2tn/Meister_2016/基板/elecrow/all.brd

## EAGLE design 基板/elecrow/all.brd (2018-05-12)

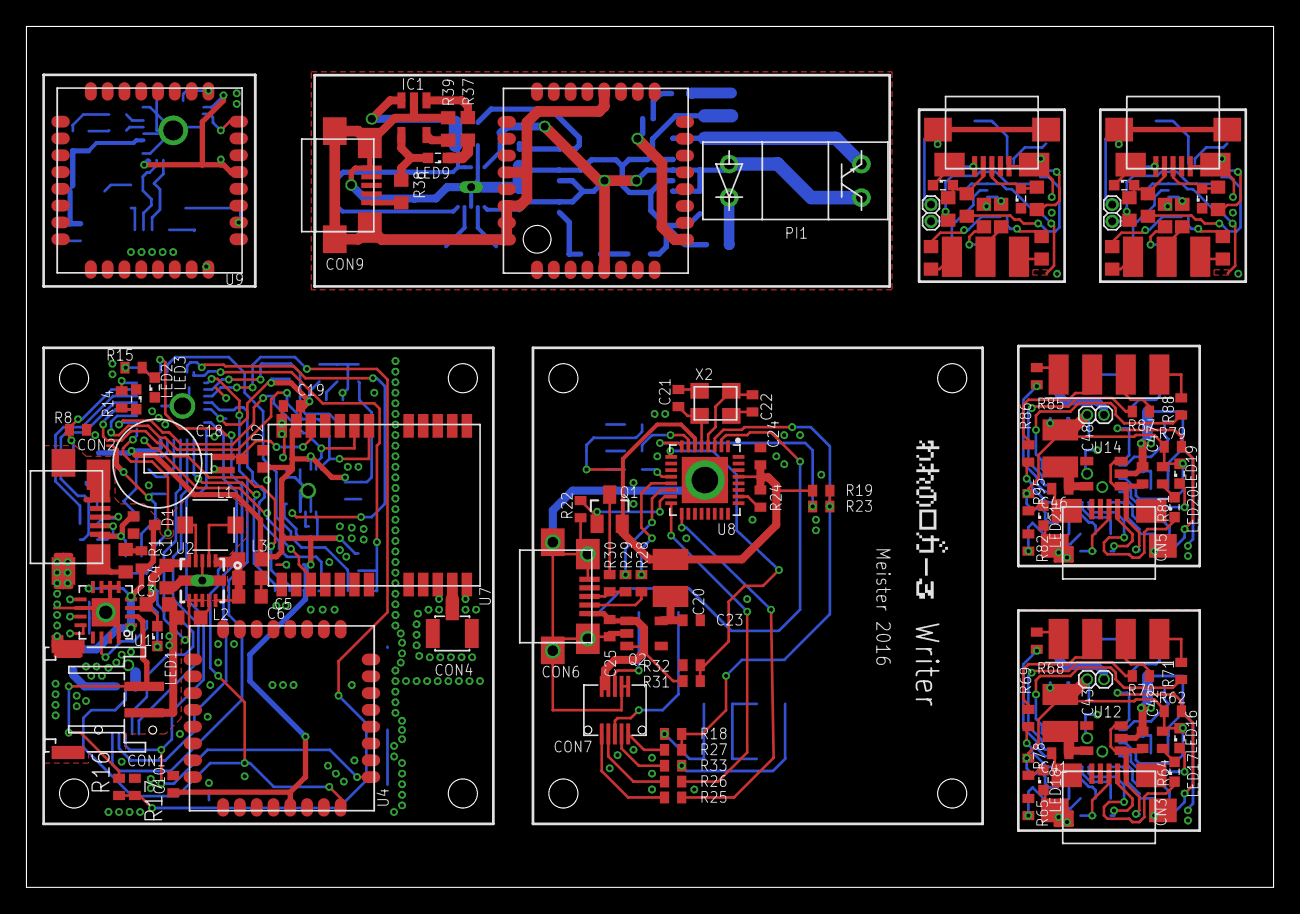
[picture p30: board all.brd from above]

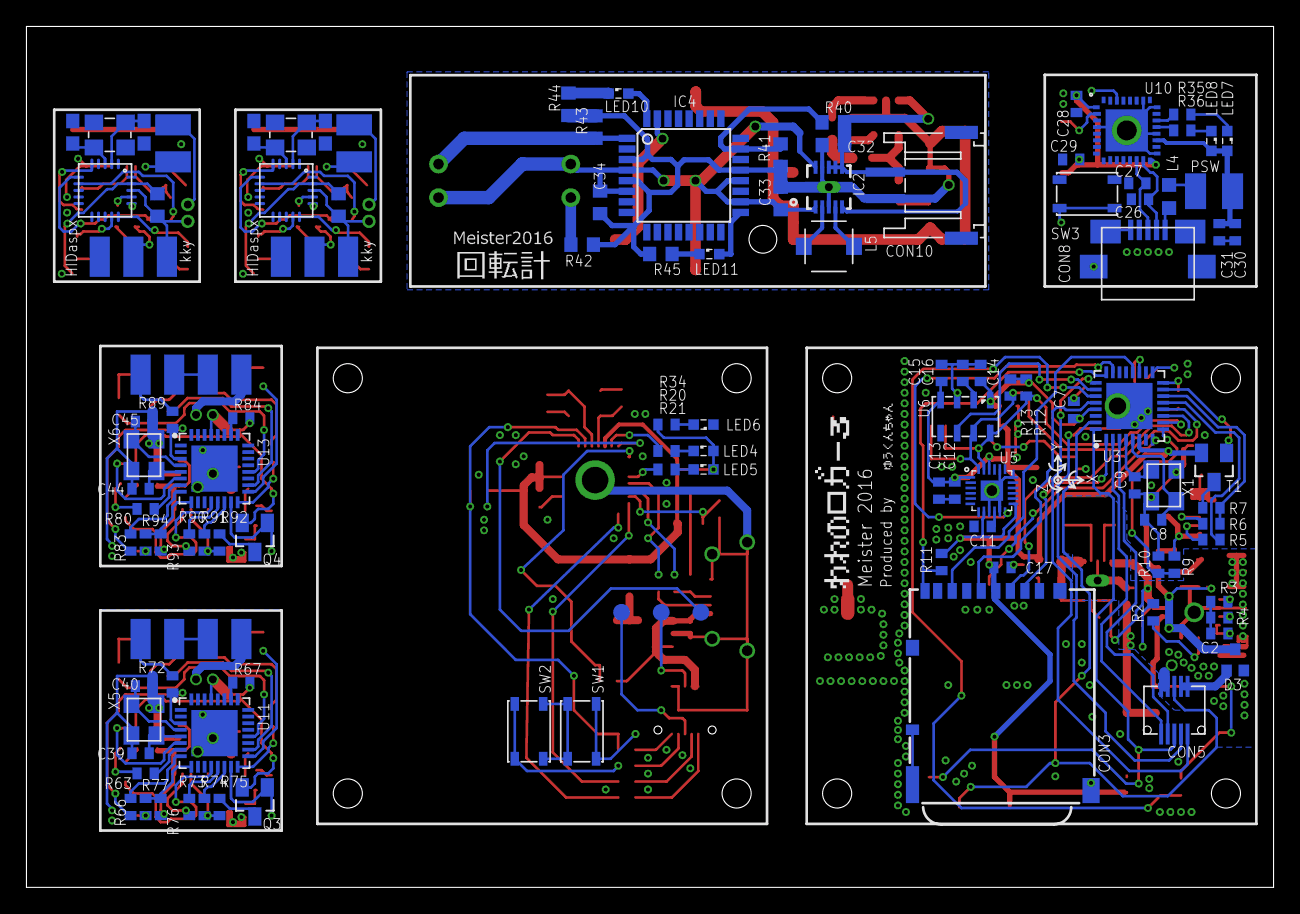
[picture p31: board all.brd from below]

Board: 2 copper layers, 94.3 x 65.1 mm, 236 parts (113 on the bottom side), 217 nets.

Parts:
C1, C3, C4, C5, C6, C32, C33: 10u; 0603
C2: 0.2u; 0402
C7, C10, C11, C12, C14, C16, C17, C19: 0.1u; 0402
C8, C9, C26, C27, C28, C29, C30, C31: 0402
C13: 10n; 0402
C15: 10u; 0402
C18: DCK-3R3E224-E
C20, C43, C48: PSW; C3225
C21, C22, C39, C40, C44, C45: 8P; C0402
C23, C25, C41, C42, C46, C47: 1u; C0402
C24: 0.1u; C0402
C34: 0.1u; 0603
C35, C36, C37, C38: 22p; C0603
CN1, CN2, CN3, CN5: ZX62R-B-5P; MICRO-B
CN4, CN6: 2X4SMD
CON1, CON10: JST-PH2
CON2, CON6, CON8, CON9: ZX62R-B-5P; MICRO-B
CON3: DM3AT-SF-PEJM5SMD; DM3AT-SF-PEJM5
CON4: U.FL; U.FL-R-SMT-1
CON5: DF12#-10DS; DF12A-10DS
CON7: DF12#-10DP; DF12D-10DP
D1, D2, D3: RB461F; UMD3
IC1: TSOT23-5
IC2: S-PVSON-N10
IC3: LITESMD; LITE
IC4: ATMEGA48/88/168-AU; TQFP32-08
JP1, JP2: 1X02/HALF
JP3, JP4: 1X02/HARF
L1, L5: 2.2u; VLF4012ST
L2, L3: BLM; C0603K
L4: C0603K
LED1, LED2, LED3, LED4, LED5, LED6, LED7, LED8, LED9, LED10, LED11, LED16, LED17, LED18, LED19, LED20, LED21: SML0603
LED12, LED13, LED14, LED15: BLUE; SML0603
PI1: RPI-574
PSW, PSW1, PSW2: 100m; C3225
Q1, Q3, Q4: PDTA114ET; SOT23
Q2: MIC550X; SOT23_5PIN
R1: 1; 0402
R2, R14, R15: 100; 0402
R3: 105k; 0402
R4: 124k; 0402
R5, R6: 33; 0402
R7: 1.5k; 0402
R8, R10: 10k; 0402
R9: 5.6k; 0402
R11, R12, R13: 4.7k; 0402
R16: 3.3k; 0402
R17: 2.2k; 0402
R18, R23, R25, R26, R27, R33, R66, R68, R69, R70, R71, R72, R83, R85, R86, R87, R88, R89: 270; R0402
R19, R22, R24, R32, R62, R65, R67, R77, R79, R82, R84, R94: 10k; R0402
R20, R21, R30, R63, R64, R75, R80, R81, R92: 1.5k; R0402
R28, R29, R73, R74, R90, R91: 33; R0402
R31, R76, R93: 5.6k; R0402
R34, R78, R95: 750; R0402
R35, R36: R0402
R37: 100; 0603
R38: 0.25; 0603
R39: 3.2k; 0603
R40: 3.3k; 0603
R41: 2.2k; 0603
R42, R44, R45: 200; 0603
R43: 1.0M; 0603
R46, R54: 2.2k; R0603
R47, R48, R55, R56: 75; R0603
R49, R57: 10k; R0603
R50, R51, R52, R53, R58, R59, R60, R61: 100; R0603
SW1, SW2, SW3: SKRPACE010
T1: PDTA114ET; SOT23
U1: LTC4055; QFN16
U2: TPS6300XDRCT; S-PVSON-N10
U3, U8, U11, U13: LPC11U35FHI33/501; SOT617-3
U4, U9: TWE-LITE_SMD; LITE
U5: MPU-9250
U6: MPL3115A2
U7: NEO-7M
U10: FT232RQ; QFN32
U12, U14: MIC550X; SOT23_5PIN
U$1: DIRECTION
U$2, U$3, U$4: TESTPAD
U$5, U$7: TINY2313-*M*; MLF20
U$6, U$8: AVR-ISP-6-EDGE; 6PAD_ISP
X1, X2, X3, X4, X5, X6: FA238V; V66RA

Connections:
!RESET!: CON5.10, U3.2
!USB_CONNECT!: R8.2, T1.1, U3.15
!USB_CONNECT!1: Q1.1, R22.2, U8.15
!USB_CONNECT!2: Q3.1, R65.2, U11.15
!USB_CONNECT!3: Q4.1, R82.2, U13.15
+3V1: C28.1, C29.1, U9.5, U10.1, U10.16
+3V2: C33.1, C34.1, IC2.1, IC2.10, IC3.5, IC4.4, IC4.6, IC4.18, IC4.20, PI1.DA, PI1.TC
+3V3: C7.1, C10.1, C12.1, C13.1, C14.1, C15.1, C17.1, C19.1, CON3.4, D2.2, L3.1, R11.2, R12.2, R13.2, T1.2, U3.6, U3.29, U4.5, U5.1, U5.8, U5.13, U5.22, U6.1, U6.4, U7.23
+5V: D1.3, D3.3, R1.2, U1.1, U1.4, U1.8
+5V1: C30.1, C31.1, LED7.A, LED8.A, PSW.1, U10.19
AD7: R16.1, R17.2, U3.27
BOOT: CON7.8, R33.2
D+USB: CON6.3, R29.2, R30.1
D+USB1: CN3.3, R74.2, R75.1
D+USB2: CN5.3, R91.2, R92.1
D-USB: CON6.2, R28.2
D-USB1: CN3.2, R73.2
D-USB2: CN5.2, R90.2
GND: C5.2, C6.2, C7.2, C8.2, C9.2, C10.2, C11.2, C12.2, C13.2, C14.2, C15.2, C16.2, C17.2, C18.1, C19.2, CON3.6, CON3.10, CON3.P$10, CON3.P$11, CON3.P$12, CON3.P$14, CON4.1, CON4.2, L2.2, LED2.C, LED3.C, R8.1, R10.1, R17.1, U2.9, U3.33, U4.20, U4.28, U4.30, U4.31, U4.32, U5.9, U5.11, U5.18, U5.20, U5.PAD, U6.3, U7.10, U7.12, U7.13, U7.24, X1.P2GND, X1.P4GND
GND1: C21.2, C22.2, C23.2, C24.2, C25.2, CON6.5, CON6.CASE@1, CON6.CASE@2, CON6.CASE@3, CON6.CASE@4, CON7.7, CON7.9, LED6.C, Q2.2, R22.1, R32.1, SW1.1, SW1.2, SW2.1, SW2.2, U8.33, X2.P2GND, X2.P4GND
GND2: C26.2, C27.2, C28.2, C29.2, C30.2, C31.2, CON8.5, CON8.CASE@1, CON8.CASE@2, CON8.CASE@3, CON8.CASE@4, SW3.1, SW3.2, U9.20, U9.28, U9.30, U9.31, U9.32, U10.4, U10.17, U10.20, U10.24, U10.26, U10.PAD
GND3: C32.2, C33.2, C34.2, CON9.5, CON9.CASE@1, CON9.CASE@2, CON9.CASE@3, CON9.CASE@4, CON10.1, IC1.2, IC2.3, IC2.9, IC2.PAD, IC2.PAD@1, IC3.20, IC3.28, IC3.30, IC3.31, IC3.32, IC4.3, IC4.5, IC4.21, R39.1, R41.1, R42.1, R43.2, R44.1, R45.1
GND4: C35.2, C36.2, CN1.5, CN1.CASE@1, CN1.CASE@2, CN1.CASE@3, CN1.CASE@4, LED12.C, LED13.C, U$5.P$8, U$6.GND, X3.P2GND, X3.P4GND
GND5: C37.2, C38.2, CN2.5, CN2.CASE@1, CN2.CASE@2, CN2.CASE@3, CN2.CASE@4, LED14.C, LED15.C, U$7.P$8, U$8.GND, X4.P2GND, X4.P4GND
GND6: C39.2, C40.2, C41.2, C42.2, CN3.5, CN3.CASE@1, CN3.CASE@2, CN3.CASE@3, CN3.CASE@4, CN4.3, CN4.5, LED18.C, R65.1, R77.1, U11.33, U12.2, X5.P2GND, X5.P4GND
GND7: C44.2, C45.2, C46.2, C47.2, CN5.5, CN5.CASE@1, CN5.CASE@2, CN5.CASE@3, CN5.CASE@4, CN6.3, CN6.5, LED21.C, R82.1, R94.1, U13.33, U14.2, X6.P2GND, X6.P4GND
MISO1: CON3.7, U3.20
MISO2: R59.1, U$7.P$15
MISO3: R51.1, U$5.P$15
MOSI1: CON3.3, U3.12
MOSI2: R58.2, U$7.P$16
MOSI3: R50.2, U$5.P$16
unnamed: C8.1, U3.5, X1.P1X1
unnamed: CON2.2, R5.1
unnamed: C9.1, U3.4, X1.P3X2
unnamed: CON2.3, R6.1
unnamed: R7.2, T1.3
unnamed: LED3.A, R15.1
unnamed: CON4.3, U7.11
unnamed: C16.1, U6.2
unnamed: L1.2, U2.2
unnamed: C11.1, U5.10
unnamed: L1.1, U2.4
unnamed: LED2.A, R14.1
unnamed: C21.1, U8.5, X2.P1X1
unnamed: C22.1, U8.4, X2.P3X2
unnamed: R29.1, U8.14
unnamed: C1.1, R1.1
unnamed: C5.1, C6.1, L3.2, U2.1, U2.10
unnamed: CON5.1, CON5.3, D3.2
unnamed: R3.2, U1.9
unnamed: R4.2, U1.11
unnamed: C2.1, U1.12
unnamed: R2.1, U1.14
unnamed: LED1.C, R2.2
unnamed: C3.1, C4.1, LED1.A, U1.3, U2.5, U2.6, U2.7, U2.8
unnamed: CON1.1, R16.2, U1.2
unnamed: C18.2, D2.3, U7.22
unnamed: R28.1, U8.13
unnamed: Q1.3, R30.2
unnamed: CON7.2, R25.1
unnamed: CON7.4, R26.1
unnamed: LED6.A, R34.2
unnamed: LED4.C, R20.1
unnamed: C20.2, C23.1, Q2.5
unnamed: CON7.10, R27.1
unnamed: R18.1, SW1.3, SW1.4
unnamed: R33.1, SW2.3, SW2.4
unnamed: U8.2, U$4.P$1
unnamed: LED5.C, R21.1
unnamed: C26.1, CON8.2, U10.15
unnamed: C27.1, CON8.3, U10.14
unnamed: CON8.1, L4.2
unnamed: U9.9, U10.30
unnamed: U9.8, U10.2
unnamed: L4.1, PSW.2
unnamed: LED7.C, R35.2
unnamed: LED8.C, R36.2
unnamed: R35.1, U10.22
unnamed: R36.1, U10.21
unnamed: SW3.3, SW3.4, U9.2
unnamed: IC1.4, LED9.A, R38.2
unnamed: IC1.1, R37.2
unnamed: LED9.C, R37.1
unnamed: IC2.4, L5.1
unnamed: IC2.2, L5.2
unnamed: CON9.1, R38.1
unnamed: IC1.5, R39.2
unnamed: IC4.23, R40.1, R41.2
unnamed: IC4.1, PI1.TE, R43.1
unnamed: PI1.DC, R42.2
unnamed: IC4.17, LED11.A
unnamed: LED11.C, R45.2
unnamed: IC4.32, LED10.A
unnamed: LED10.C, R44.2
unnamed: C36.1, U$5.P$2, X3.P1X1
unnamed: C35.1, U$5.P$3, X3.P3X2
unnamed: CN1.1, PSW1.2
unnamed: CN1.2, LED13.A, R46.2, R47.2
unnamed: CN1.3, LED12.A, R48.2
unnamed: R46.1, U$5.P$7
unnamed: R47.1, U$5.P$6
unnamed: R48.1, U$5.P$5
unnamed: R49.2, U$5.P$19
unnamed: R52.2, U$6.SCK
unnamed: R51.2, U$6.MISO
unnamed: R53.2, U$6.RST
unnamed: R50.1, U$6.MOSI
unnamed: JP1.2, PSW1.1
unnamed: C38.1, U$7.P$2, X4.P1X1
unnamed: C37.1, U$7.P$3, X4.P3X2
unnamed: CN2.1, PSW2.2
unnamed: CN2.2, LED15.A, R54.2, R55.2
unnamed: CN2.3, LED14.A, R56.2
unnamed: R54.1, U$7.P$7
unnamed: R55.1, U$7.P$6
unnamed: R56.1, U$7.P$5
unnamed: R57.2, U$7.P$19
unnamed: R60.2, U$8.SCK
unnamed: R59.2, U$8.MISO
unnamed: R61.2, U$8.RST
unnamed: R58.1, U$8.MOSI
unnamed: JP2.2, PSW2.1
unnamed: C39.1, U11.5, X5.P1X1
unnamed: C40.1, U11.4, X5.P3X2
unnamed: R74.1, U11.14
unnamed: R73.1, U11.13
unnamed: Q3.3, R75.2
unnamed: CN4.2, R68.1
unnamed: CN4.4, R69.1
unnamed: CN4.6, R70.1
unnamed: CN4.8, R71.1
unnamed: LED18.A, R78.2
unnamed: LED17.A, R64.2
unnamed: LED16.C, R63.1
unnamed: C41.1, C43.2, U12.5
unnamed: CN4.7, R72.1
unnamed: CN4.1, JP3.1
unnamed: C44.1, U13.5, X6.P1X1
unnamed: C45.1, U13.4, X6.P3X2
unnamed: R91.1, U13.14
unnamed: R90.1, U13.13
unnamed: Q4.3, R92.2
unnamed: CN6.2, R85.1
unnamed: CN6.4, R86.1
unnamed: CN6.6, R87.1
unnamed: CN6.8, R88.1
unnamed: LED21.A, R95.2
unnamed: LED20.A, R81.2
unnamed: LED19.C, R80.1
unnamed: C46.1, C48.2, U14.5
unnamed: CN6.7, R89.1
unnamed: CN6.1, JP4.1
PGND: C1.2, C2.2, C3.2, C4.2, CON1.2, CON1.PAD1, CON1.PAD2, CON2.5, CON2.CASE@1, CON2.CASE@2, CON2.CASE@3, CON2.CASE@4, CON5.7, CON5.9, L2.1, R3.1, R4.1, U1.5, U1.6, U1.7, U1.10, U1.16, U1.PAD, U2.3, U2.PAD, U2.PAD@1
PIO0_1: CON5.8, U3.3
PIO0_2: U3.8, U7.3
PIO0_3: R23.2, U8.8
PIO0_4: R24.1, U8.26
PIO0_5: R66.2, U11.8
PIO0_6: LED17.C, U11.12
PIO0_7: R14.2, U3.16
PIO0_8: R15.2, U3.17
PIO0_9: R67.1, U11.26
PIO0_10: R63.2, U11.7
PIO0_11: R83.2, U13.8
PIO0_12: LED20.C, U13.12
PIO0_13: U3.23, U5.12
PIO0_14: CON3.9, R11.1, U3.24
PIO0_15: R84.1, U13.26
PIO0_16: U3.26, U6.6
PIO0_17: R80.2, U13.7
PIO0_20: R20.2, U8.7
PIO0_21: R21.2, U8.12
PIO1_19: CON3.2, U3.1
RST1: R61.1, U$7.P$14
RST2: R53.1, U$5.P$14
RXD: CON5.5, U3.31, U4.8
RXD1: CON7.5, U$3.P$1
SCK1: CON3.5, U3.28
SCK2: R60.1, U$7.P$17
SCK3: R52.1, U$5.P$17
SCL: R12.1, U3.10, U5.23, U6.8, U7.19
SDA: R13.1, U3.11, U5.24, U6.7, U7.18
SWCLK: CON5.4, U3.19
SWDIO: CON5.2, U3.25
TARGET_!RESET!: R18.2, R19.2, R23.1, R27.2, U8.3
TARGET_!RESET!1: R62.2, R66.1, R72.2, U11.3
TARGET_!RESET!2: R79.2, R83.1, R89.2, U13.3
TARGET_SWCLK: R26.2, U8.16
TARGET_SWCLK1: R69.2, U11.16
TARGET_SWCLK2: R86.2, U13.16
TARGET_SWDIO: R25.2, U8.17
TARGET_SWDIO1: R68.2, U11.17
TARGET_SWDIO2: R85.2, U13.17
TARGET_SWO: R70.2, U11.18
TARGET_SWO1: R87.2, U13.18
TARGET_TDI: R71.2, U11.20
TARGET_TDI1: R88.2, U13.20
TXD: CON5.6, U3.32, U4.9
TXD1: CON7.6, U$2.P$1
U3: IC3.9, IC4.31
USB_D+: R6.2, R7.1, U3.14
USB_D-: R5.2, U3.13
USB_VBUS: R9.1, R10.2, U3.9
USB_VBUS1: R31.1, R32.2, U8.9
USB_VBUS2: R76.1, R77.2, U11.9
USB_VBUS3: R93.1, R94.2, U13.9
VBUS: CON2.1, D1.2, R9.2
VCC: C25.1, CON6.1, CON7.1, CON7.3, Q2.1, Q2.3, R31.2
VCC1: C32.1, CON10.2, IC1.3, IC2.5, IC2.6, IC2.7, IC2.8, R40.2
VCC2: JP1.1, R49.1, U$5.P$18, U$6.VCC
VCC3: JP2.1, R57.1, U$7.P$18, U$8.VCC
VCC4: C42.1, CN3.1, R76.2, U12.1, U12.3
VCC5: C47.1, CN5.1, R93.2, U14.1, U14.3
VDD: C20.1, C24.1, LED4.A, LED5.A, Q1.2, R19.1, R24.2, R34.1, U8.6, U8.29
VDD1: C43.1, JP3.2, LED16.A, Q3.2, R62.1, R64.1, R67.2, R78.1, U11.6, U11.29
VDD2: C48.1, JP4.2, LED19.A, Q4.2, R79.1, R81.1, R84.2, R95.1, U13.6, U13.29
